Abdul-Hakim88/STM32-BLUE-PILL/3D Views/PCB1.png

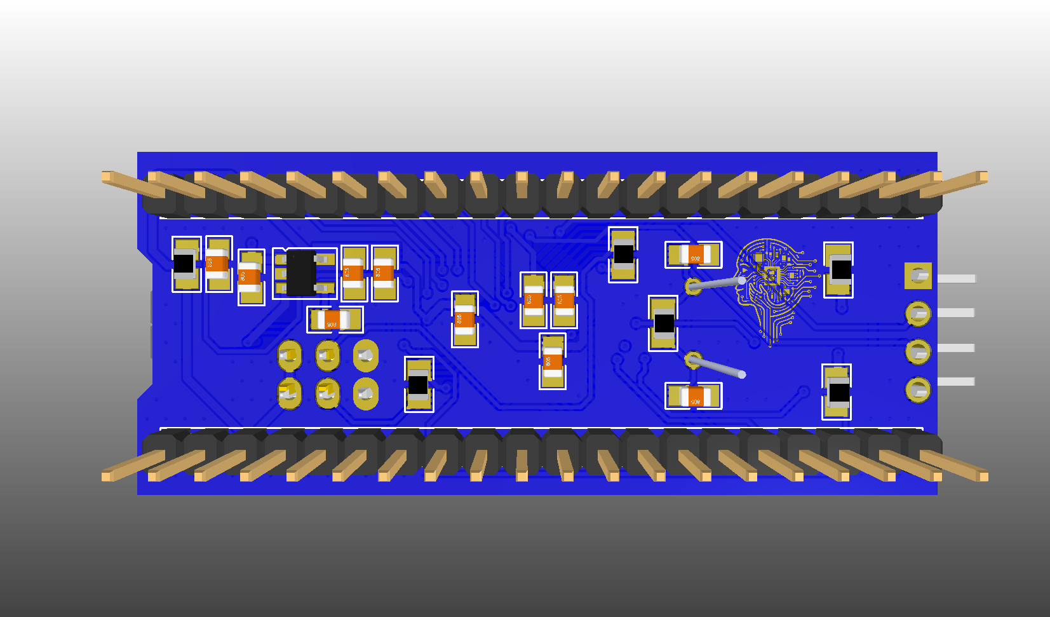
3D Views/PCB1.png
