Abdul-Hakim88/STM32-BLUE-PILL/Layout/2D1.png

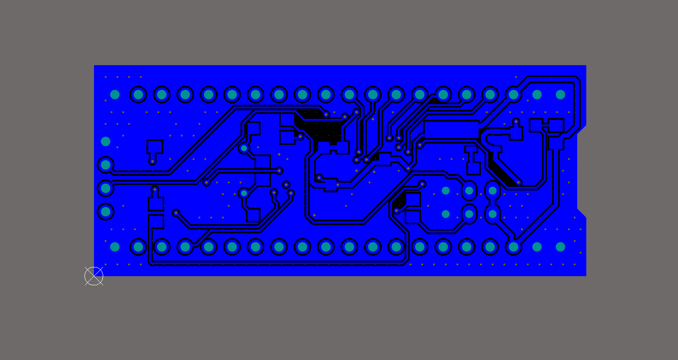
Layout/2D1.png
